momu/esp32-alarmlicht/hardware/esp32-alarmlicht.kicad_sch

## KiCad design hardware/esp32-alarmlicht.kicad_sch (2023-11-09, an earlier design)

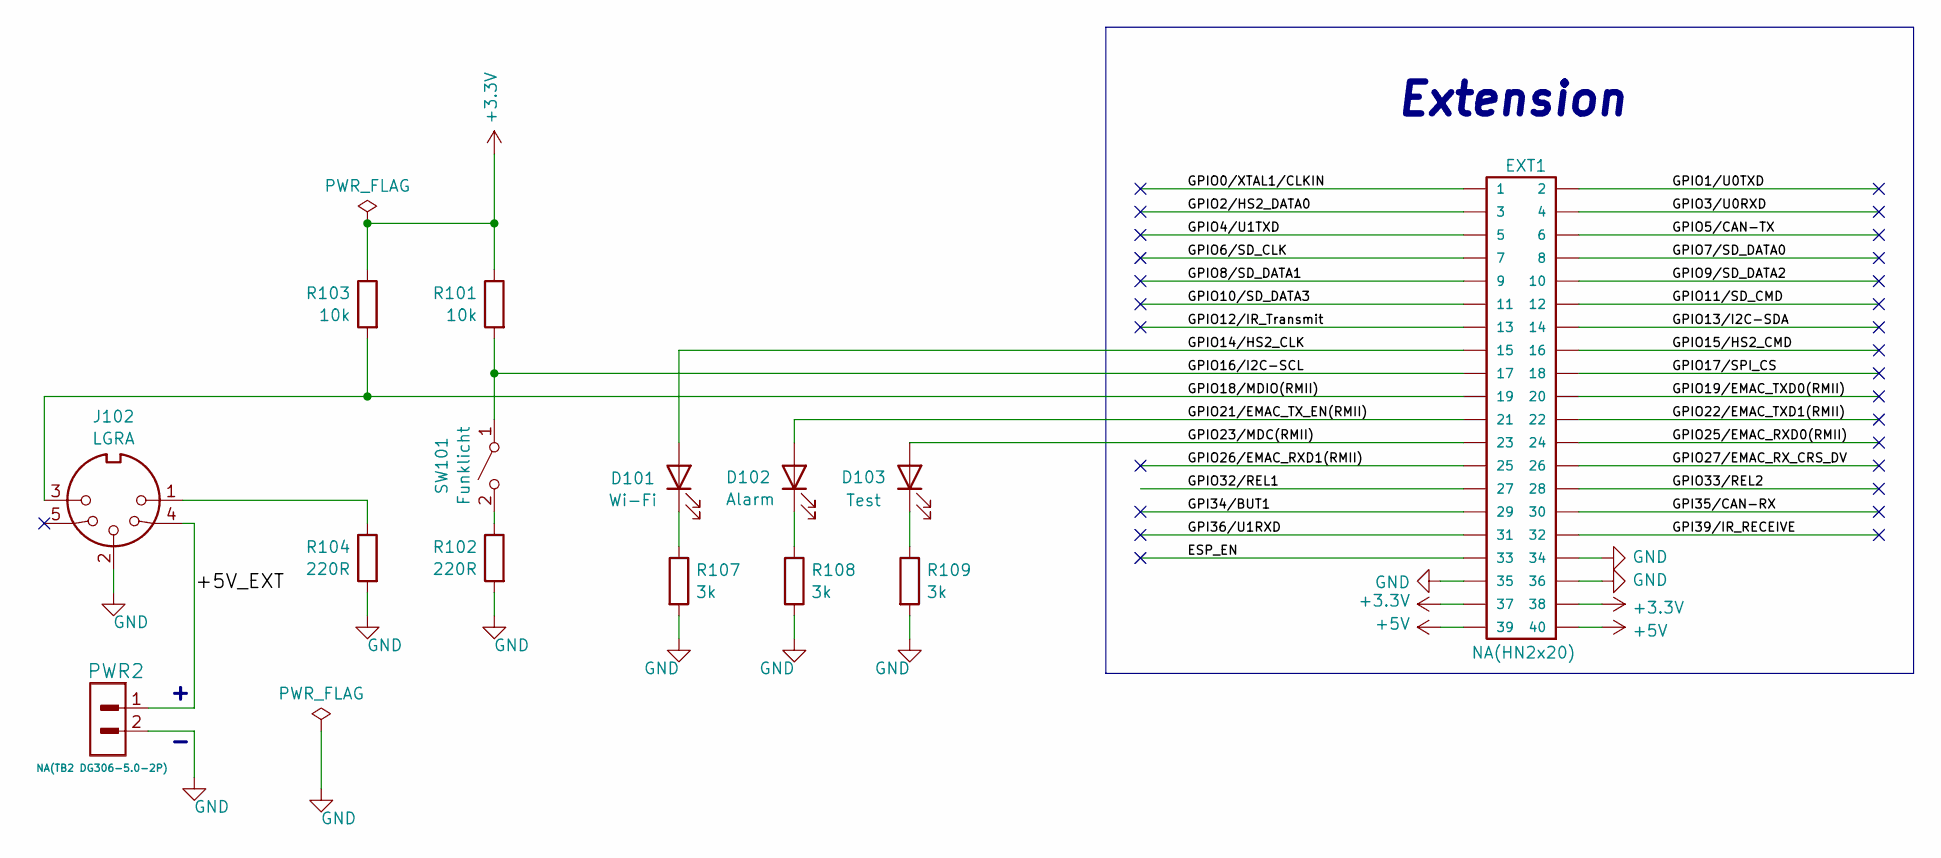
[picture p7: schematic esp32-alarmlicht.kicad_sch]

Parts:
D101: Wi-Fi
D102: Alarm
D103: Test
EXT1: NA(HN2x20); HN2x20
J102: LGRA
PWR2: NA(TB2 DG306-5.0-2P); TB2-DG306-5.0_2P
R101, R103: 10k
R102, R104: 220R
R107, R108, R109: 3k
SW101: Funklicht

Connections:
+3.3V: EXT1.37, EXT1.38, R101.1, R103.1
+5V: EXT1.39, EXT1.40
+5V_EXT: J102.4, PWR2.1
ESP_EN: EXT1.33
GND: EXT1.34, EXT1.35, EXT1.36, J102.2, PWR2.2, R102.2, R104.2, R107.2, R108.2, R109.2
GPI34/BUT1: EXT1.29
GPI35/CAN-RX: EXT1.30
GPI36/U1RXD: EXT1.31
GPI39/IR_RECEIVE: EXT1.32
GPIO0/XTAL1/CLKIN: EXT1.1
GPIO1/U0TXD: EXT1.2
GPIO2/HS2_DATA0: EXT1.3
GPIO3/U0RXD: EXT1.4
GPIO4/U1TXD: EXT1.5
GPIO5/CAN-TX: EXT1.6
GPIO6/SD_CLK: EXT1.7
GPIO7/SD_DATA0: EXT1.8
GPIO8/SD_DATA1: EXT1.9
GPIO9/SD_DATA2: EXT1.10
GPIO10/SD_DATA3: EXT1.11
GPIO11/SD_CMD: EXT1.12
GPIO12/IR_Transmit: EXT1.13
GPIO13/I2C-SDA: EXT1.14
GPIO14/HS2_CLK: D101.2 (A), EXT1.15
GPIO15/HS2_CMD: EXT1.16
GPIO16/I2C-SCL: EXT1.17, R101.2, SW101.1 (A)
GPIO17/SPI_CS: EXT1.18
GPIO18/MDIO(RMII): EXT1.19, J102.3, R103.2
GPIO19/EMAC_TXD0(RMII): EXT1.20
GPIO21/EMAC_TX_EN(RMII): D102.2 (A), EXT1.21
GPIO22/EMAC_TXD1(RMII): EXT1.22
GPIO23/MDC(RMII): D103.2 (A), EXT1.23
GPIO25/EMAC_RXD0(RMII): EXT1.24
GPIO26/EMAC_RXD1(RMII): EXT1.25
GPIO27/EMAC_RX_CRS_DV: EXT1.26
GPIO32/REL1: EXT1.27
GPIO33/REL2: EXT1.28
unnamed: D101.1 (K), R107.1
unnamed: D102.1 (K), R108.1
unnamed: D103.1 (K), R109.1
unnamed: J102.1, R104.1
unnamed: R102.1, SW101.2 (B)

Notes on the sheet:
Extension
